s-l893/Automotive-Telemetry-Data-Acquisition-System-Black-Box-/BlackBox_V2/Core/Src/display.c

/*
 * display.c
 *
 *  Created on: Sep 11, 2026
 *      Author: Sunny Lin
 */
#include "display.h"
#include "main.h"
#include "spi.h"
#include "sd_spi_bus.h"
#include "iwdg.h"

#include <stdint.h>

#define DISPLAY_CS_PIN        GPIO_PIN_14
#define DISPLAY_CS_GPIO_PORT  GPIOB
#define DISPLAY_DC_PIN        DC_SPI1_Pin
#define DISPLAY_DC_GPIO_PORT  DC_SPI1_GPIO_Port
#define DISPLAY_RST_PIN       RESET_SPI1_Pin
#define DISPLAY_RST_GPIO_PORT RESET_SPI1_GPIO_Port
#define NATIVE_WIDTH 240
#define NATIVE_HEIGHT 320
#define LOGICAL_WIDTH  320  // done for custom function to remap points as bitwise toggle for MV MADCT1 doesnt work on chinese branded ili9341
#define LOGICAL_HEIGHT 240

/*
 * LCD bring-up notes:
 * - Nucleo: SB13/SB14 OFF, SB62/SB63 ON so PA2/PA3 reach the headers (HW).
 * - PA2/PA3 are LCD DC/RESET — do not enable USART2 on those pins.
 * - SD disk init leaves SPI1 in Mode3 — reconfig Mode0 before LCD traffic.
 * - Fill buffer is static: default MSP stack is only 1KB.
 * - PB14 (LCD_CS) is in the .ioc but was never emitted into gpio.c.
 */

static void LCD_BusPrepare(void) // SPI1 back into mode 0
{
	GPIO_InitTypeDef GPIO_InitStruct = {0};

	/* USART2 must not own PA2/PA3 (DC/RESET) */
	__HAL_RCC_USART2_CLK_ENABLE();
	__HAL_RCC_USART2_FORCE_RESET();
	__HAL_RCC_USART2_RELEASE_RESET();
	__HAL_RCC_USART2_CLK_DISABLE();

	SD_CS_ForceIdleHigh();

	__HAL_RCC_GPIOA_CLK_ENABLE();
	__HAL_RCC_GPIOB_CLK_ENABLE();

	HAL_GPIO_WritePin(DISPLAY_CS_GPIO_PORT, DISPLAY_CS_PIN, GPIO_PIN_SET);
	HAL_GPIO_WritePin(DISPLAY_DC_GPIO_PORT, DISPLAY_DC_PIN, GPIO_PIN_RESET);
	HAL_GPIO_WritePin(DISPLAY_RST_GPIO_PORT, DISPLAY_RST_PIN, GPIO_PIN_SET);

	GPIO_InitStruct.Pin = DISPLAY_CS_PIN;
	GPIO_InitStruct.Mode = GPIO_MODE_OUTPUT_PP;
	GPIO_InitStruct.Pull = GPIO_NOPULL;
	GPIO_InitStruct.Speed = GPIO_SPEED_FREQ_HIGH;
	HAL_GPIO_Init(DISPLAY_CS_GPIO_PORT, &GPIO_InitStruct);

	GPIO_InitStruct.Pin = DISPLAY_DC_PIN | DISPLAY_RST_PIN;
	GPIO_InitStruct.Speed = GPIO_SPEED_FREQ_LOW;
	HAL_GPIO_Init(DISPLAY_DC_GPIO_PORT, &GPIO_InitStruct);
	GPIOA->AFR[0] &= ~(0xFFu << (2 * 4)); /* clear USART2 AF on PA2/PA3 */

	/* ILI9341: SPI Mode0 (SD path may have left Mode3) */
	SD_SPI_Reconfig(SPI_BAUDRATEPRESCALER_8, SPI_POLARITY_LOW, SPI_PHASE_1EDGE);
}

/* HELPER GPIO TOGGLE FUNCTIONS FOR CS, DC, RESET */

static void LCD_CS_High(void)
{
	HAL_GPIO_WritePin(DISPLAY_CS_GPIO_PORT, DISPLAY_CS_PIN, GPIO_PIN_SET);
}

static void LCD_CS_Low(void)
{
	HAL_GPIO_WritePin(DISPLAY_CS_GPIO_PORT, DISPLAY_CS_PIN, GPIO_PIN_RESET);
}

static void LCD_DC_High(void)	/* DC REQUIRED TO BE PULLED HIGH FOR DATA */
{
	HAL_GPIO_WritePin(DISPLAY_DC_GPIO_PORT, DISPLAY_DC_PIN, GPIO_PIN_SET);
}

static void LCD_DC_Low(void)	/* DC REQUIRED TO BE PULLED LOW FOR COMMANDS */
{
	HAL_GPIO_WritePin(DISPLAY_DC_GPIO_PORT, DISPLAY_DC_PIN, GPIO_PIN_RESET);
}

static void LCD_RST_Low(void)
{
	HAL_GPIO_WritePin(DISPLAY_RST_GPIO_PORT, DISPLAY_RST_PIN, GPIO_PIN_RESET);
}

static void LCD_RST_High(void)
{
	HAL_GPIO_WritePin(DISPLAY_RST_GPIO_PORT, DISPLAY_RST_PIN, GPIO_PIN_SET);
}

/* SEND BYTE TO ILI9341 */
void LCD_Send_Command(uint8_t cmd, uint8_t *params, int param_count)
{
	SD_SPI_Reconfig(SPI_BAUDRATEPRESCALER_8, SPI_POLARITY_LOW, SPI_PHASE_1EDGE); // toggle spi1 back to mode 0
	LCD_CS_Low();
	LCD_DC_Low();
	HAL_SPI_Transmit(&hspi1, &cmd, 1, HAL_MAX_DELAY);
	if (param_count > 0) {
		LCD_DC_High();
		HAL_SPI_Transmit(&hspi1, params, param_count, HAL_MAX_DELAY);
	}
	LCD_CS_High();
}

void LCD_Hardware_Reset(void) // ILI9341 power up sequence
{
	LCD_RST_Low();
	HAL_Delay(15);
	LCD_RST_High();
	HAL_Delay(120);
}

void LCD_Init(void)
{
	LCD_BusPrepare();
	LCD_Hardware_Reset();
	LCD_Send_Command(0x11, NULL, 0);
	HAL_Delay(120); /* blocking delays used in init sequence (reset included) */
	uint8_t pixel_format = 0x55;
	LCD_Send_Command(0x3A, &pixel_format, 1);
	uint8_t madct1 = 0x48;
	LCD_Send_Command(0x36, &madct1, 1);
	LCD_Send_Command(0x29, NULL, 0);
	HAL_Delay(33);
}

void LCD_SetWindow(uint16_t x0, uint16_t y0, uint16_t x1, uint16_t y1)
{
	uint8_t col_params[4];
	/* fill col_params using x0/x1 high/low bytes, send via 0x2A (CASET) */
	col_params[0] = x0 >> 8;
	col_params[1] = x0 & 0xFF;
	col_params[2] = x1 >> 8;
	col_params[3] = x1 & 0xFF;
	LCD_Send_Command(0x2A, col_params, 4);
	uint8_t row_params[4];
	row_params[0] = y0 >> 8;
	row_params[1] = y0 & 0xFF;
	row_params[2] = y1 >> 8;
	row_params[3] = y1 & 0xFF;
	LCD_Send_Command(0x2B, row_params, 4);
	/* fill row_params using y0/y1 high/low bytes, send via 0x2B (PASET) */
}

void LCD_SetWindow_Logical(uint16_t lx0, uint16_t ly0, uint16_t lx1, uint16_t ly1){
	uint16_t x0_start = lx0;
	uint16_t y0_start = ly0;
	uint16_t x1_start = lx1;
	uint16_t y1_start = ly1;

	uint16_t x0_end = (LOGICAL_HEIGHT - 1) - y0_start;
	uint16_t y0_end = ((NATIVE_HEIGHT - 1) - x0_start);

	uint16_t x1_end = (LOGICAL_HEIGHT - 1) - y1_start;
	uint16_t y1_end = ((NATIVE_HEIGHT - 1) - x1_start); 	// consistent formula for a 90 degree rotation

	if(y1_end < y0_end){		// ensures correct coordinate order
		uint16_t temp = y1_end;
		y1_end = y0_end;
		y0_end = temp;
	}

	if(x1_end < x0_end){		// ensures correct coordinate order
		uint16_t temp = x1_end;
		x1_end = x0_end;
		x0_end = temp;
	}

	LCD_SetWindow(x0_end, y0_end, x1_end, y1_end);
}

static void LCD_Send_Data(uint8_t *data, uint32_t size)
{
	HAL_SPI_Transmit(&hspi1, data, size, HAL_MAX_DELAY);
}

void LCD_FillScreen(uint16_t colour)
{
	/* static: 640B on a 1KB MSP stack HardFaults mid-fill */
	static uint8_t colour_buffer[640];
	uint8_t ramwr = 0x2C;
	int k;

	LCD_SetWindow_Logical(0, 0, LOGICAL_WIDTH - 1, LOGICAL_HEIGHT - 1);

	LCD_CS_Low();
	LCD_DC_Low();
	HAL_SPI_Transmit(&hspi1, &ramwr, 1, HAL_MAX_DELAY);
	LCD_DC_High();

	/* SPLIT UINT16T VARIABLE INTO UINT8T INTO ARRAY — one row (320 px) */
	for (k = 0; k < 640; k++) {
		if (k % 2 == 0) {
			colour_buffer[k] = colour >> 8;
		} else {
			colour_buffer[k] = colour & 0xFF;
		}
	}

	for (k = 0; k < LOGICAL_HEIGHT; k++) {
		LCD_Send_Data(colour_buffer, 640);
		if ((k & 0x1F) == 0) {
			HAL_IWDG_Refresh(&hiwdg);
		}
	}

	LCD_CS_High();
}

void LCD_FillRect(uint16_t x, uint16_t y, uint16_t w, uint16_t h, uint16_t colour){
	LCD_SetWindow_Logical(x, y, x + w - 1, y + h - 1);
	uint8_t ramwr = 0x2C;
	LCD_CS_Low();
	LCD_DC_Low();
	HAL_SPI_Transmit(&hspi1, &ramwr, 1, HAL_MAX_DELAY); // memory write mode
	LCD_DC_High();
	static uint8_t rect[2000]; // colour data for rectangle
	for (int i = 0; i < 2000; i++){
		if (i % 2 == 0){
			rect[i] = colour >> 8;
		}
		else{
			rect[i] = colour & 0xFF;

		}
	}
	uint32_t total_bytes = w * h * 2;
	uint32_t full_chunks = total_bytes / 2000;
	uint32_t leftover = total_bytes % 2000;

	for (int k = 0; k < full_chunks; k++){
		LCD_Send_Data(rect, 2000);
		if (k % 32 == 0){
			HAL_IWDG_Refresh(&hiwdg);
		}
	}

	if (leftover != 0){
		LCD_Send_Data(rect, leftover);
	}


	LCD_CS_High();
}

void LCD_DrawRect(uint16_t x, uint16_t y, uint16_t w, uint16_t h, uint16_t colour)
{
	if (w == 0 || h == 0) {
		return;
	}
	LCD_FillRect(x, y, w, 1, colour);
	LCD_FillRect(x, (uint16_t)(y + h - 1), w, 1, colour);
	LCD_FillRect(x, y, 1, h, colour);
	LCD_FillRect((uint16_t)(x + w - 1), y, 1, h, colour);
}

/* 8x8 GLCD-style font (ASCII 32..127): each byte is a column, bit0 = top */
static const uint8_t font8x8_basic[96][8] = {
	{0x00,0x00,0x00,0x00,0x00,0x00,0x00,0x00}, {0x00,0x00,0x5F,0x00,0x00,0x00,0x00,0x00},
	{0x00,0x07,0x00,0x07,0x00,0x00,0x00,0x00}, {0x14,0x7F,0x14,0x7F,0x14,0x00,0x00,0x00},
	{0x24,0x2A,0x7F,0x2A,0x12,0x00,0x00,0x00}, {0x23,0x13,0x08,0x64,0x62,0x00,0x00,0x00},
	{0x36,0x49,0x55,0x22,0x50,0x00,0x00,0x00}, {0x00,0x05,0x03,0x00,0x00,0x00,0x00,0x00},
	{0x00,0x1C,0x22,0x41,0x00,0x00,0x00,0x00}, {0x00,0x41,0x22,0x1C,0x00,0x00,0x00,0x00},
	{0x08,0x2A,0x1C,0x2A,0x08,0x00,0x00,0x00}, {0x08,0x08,0x3E,0x08,0x08,0x00,0x00,0x00},
	{0x00,0x50,0x30,0x00,0x00,0x00,0x00,0x00}, {0x08,0x08,0x08,0x08,0x08,0x00,0x00,0x00},
	{0x00,0x60,0x60,0x00,0x00,0x00,0x00,0x00}, {0x20,0x10,0x08,0x04,0x02,0x00,0x00,0x00},
	{0x3E,0x51,0x49,0x45,0x3E,0x00,0x00,0x00}, {0x00,0x42,0x7F,0x40,0x00,0x00,0x00,0x00},
	{0x42,0x61,0x51,0x49,0x46,0x00,0x00,0x00}, {0x21,0x41,0x45,0x4B,0x31,0x00,0x00,0x00},
	{0x18,0x14,0x12,0x7F,0x10,0x00,0x00,0x00}, {0x27,0x45,0x45,0x45,0x39,0x00,0x00,0x00},
	{0x3C,0x4A,0x49,0x49,0x30,0x00,0x00,0x00}, {0x01,0x71,0x09,0x05,0x03,0x00,0x00,0x00},
	{0x36,0x49,0x49,0x49,0x36,0x00,0x00,0x00}, {0x06,0x49,0x49,0x29,0x1E,0x00,0x00,0x00},
	{0x00,0x36,0x36,0x00,0x00,0x00,0x00,0x00}, {0x00,0x56,0x36,0x00,0x00,0x00,0x00,0x00},
	{0x00,0x08,0x14,0x22,0x41,0x00,0x00,0x00}, {0x14,0x14,0x14,0x14,0x14,0x00,0x00,0x00},
	{0x41,0x22,0x14,0x08,0x00,0x00,0x00,0x00}, {0x02,0x01,0x51,0x09,0x06,0x00,0x00,0x00},
	{0x32,0x49,0x79,0x41,0x3E,0x00,0x00,0x00}, {0x7E,0x11,0x11,0x11,0x7E,0x00,0x00,0x00},
	{0x7F,0x49,0x49,0x49,0x36,0x00,0x00,0x00}, {0x3E,0x41,0x41,0x41,0x22,0x00,0x00,0x00},
	{0x7F,0x41,0x41,0x22,0x1C,0x00,0x00,0x00}, {0x7F,0x49,0x49,0x49,0x41,0x00,0x00,0x00},
	{0x7F,0x09,0x09,0x09,0x01,0x00,0x00,0x00}, {0x3E,0x41,0x49,0x49,0x7A,0x00,0x00,0x00},
	{0x7F,0x08,0x08,0x08,0x7F,0x00,0x00,0x00}, {0x00,0x41,0x7F,0x41,0x00,0x00,0x00,0x00},
	{0x20,0x40,0x41,0x3F,0x01,0x00,0x00,0x00}, {0x7F,0x08,0x14,0x22,0x41,0x00,0x00,0x00},
	{0x7F,0x40,0x40,0x40,0x40,0x00,0x00,0x00}, {0x7F,0x02,0x0C,0x02,0x7F,0x00,0x00,0x00},
	{0x7F,0x04,0x08,0x10,0x7F,0x00,0x00,0x00}, {0x3E,0x41,0x41,0x41,0x3E,0x00,0x00,0x00},
	{0x7F,0x09,0x09,0x09,0x06,0x00,0x00,0x00}, {0x3E,0x41,0x51,0x21,0x5E,0x00,0x00,0x00},
	{0x7F,0x09,0x19,0x29,0x46,0x00,0x00,0x00}, {0x46,0x49,0x49,0x49,0x31,0x00,0x00,0x00},
	{0x01,0x01,0x7F,0x01,0x01,0x00,0x00,0x00}, {0x3F,0x40,0x40,0x40,0x3F,0x00,0x00,0x00},
	{0x1F,0x20,0x40,0x20,0x1F,0x00,0x00,0x00}, {0x3F,0x40,0x38,0x40,0x3F,0x00,0x00,0x00},
	{0x63,0x14,0x08,0x14,0x63,0x00,0x00,0x00}, {0x07,0x08,0x70,0x08,0x07,0x00,0x00,0x00},
	{0x61,0x51,0x49,0x45,0x43,0x00,0x00,0x00}, {0x00,0x7F,0x41,0x41,0x00,0x00,0x00,0x00},
	{0x02,0x04,0x08,0x10,0x20,0x00,0x00,0x00}, {0x00,0x41,0x41,0x7F,0x00,0x00,0x00,0x00},
	{0x04,0x02,0x01,0x02,0x04,0x00,0x00,0x00}, {0x40,0x40,0x40,0x40,0x40,0x00,0x00,0x00},
	{0x00,0x01,0x02,0x04,0x00,0x00,0x00,0x00}, {0x20,0x54,0x54,0x54,0x78,0x00,0x00,0x00},
	{0x7F,0x48,0x44,0x44,0x38,0x00,0x00,0x00}, {0x38,0x44,0x44,0x44,0x20,0x00,0x00,0x00},
	{0x38,0x44,0x44,0x48,0x7F,0x00,0x00,0x00}, {0x38,0x54,0x54,0x54,0x18,0x00,0x00,0x00},
	{0x08,0x7E,0x09,0x01,0x02,0x00,0x00,0x00}, {0x08,0x14,0x54,0x54,0x3C,0x00,0x00,0x00},
	{0x7F,0x08,0x04,0x04,0x78,0x00,0x00,0x00}, {0x00,0x44,0x7D,0x40,0x00,0x00,0x00,0x00},
	{0x20,0x40,0x44,0x3D,0x00,0x00,0x00,0x00}, {0x7F,0x10,0x28,0x44,0x00,0x00,0x00,0x00},
	{0x00,0x41,0x7F,0x40,0x00,0x00,0x00,0x00}, {0x7C,0x04,0x18,0x04,0x78,0x00,0x00,0x00},
	{0x7C,0x08,0x04,0x04,0x78,0x00,0x00,0x00}, {0x38,0x44,0x44,0x44,0x38,0x00,0x00,0x00},
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
};

void LCD_DrawChar(uint16_t x, uint16_t y, char c, uint16_t fg, uint16_t bg, uint8_t scale)
{
	uint8_t ramwr = 0x2C;
	uint16_t gw;
	uint16_t gh;
	const uint8_t *glyph;
	uint8_t strip[80];
	uint8_t fg_hi = (uint8_t)(fg >> 8);
	uint8_t fg_lo = (uint8_t)(fg & 0xFF);
	uint8_t bg_hi = (uint8_t)(bg >> 8);
	uint8_t bg_lo = (uint8_t)(bg & 0xFF);

	if (scale == 0) {
		scale = 1;
	}
	if (scale > 5) {
		scale = 5;
	}
	if (c < 32 || c > 127) {
		c = '?';
	}

	glyph = font8x8_basic[c - 32];
	gw = (uint16_t)(8U * scale);
	gh = (uint16_t)(8U * scale);

	if ((uint32_t)x + gw > LCD_WIDTH || (uint32_t)y + gh > LCD_HEIGHT) {
		return;
	}

	/*
	 * SetWindow_Logical maps landscape -> native with both axes inverted.
	 * Hardware fill order is columns right->left, within each column bottom->top.
	 */
	LCD_SetWindow_Logical(x, y, (uint16_t)(x + gw - 1U), (uint16_t)(y + gh - 1U));
	LCD_CS_Low();
	LCD_DC_Low();
	HAL_SPI_Transmit(&hspi1, &ramwr, 1, HAL_MAX_DELAY);
	LCD_DC_High();

	for (int8_t col = 7; col >= 0; col--) {
		for (int8_t sx = (int8_t)scale - 1; sx >= 0; sx--) {
			uint16_t o = 0;
			for (int8_t row = 7; row >= 0; row--) {
				uint8_t on = (glyph[(uint8_t)col] & (1U << (uint8_t)row)) ? 1U : 0U;
				uint8_t hi = on ? fg_hi : bg_hi;
				uint8_t lo = on ? fg_lo : bg_lo;
				for (int8_t sy = (int8_t)scale - 1; sy >= 0; sy--) {
					strip[o++] = hi;
					strip[o++] = lo;
					(void)sy;
				}
			}
			LCD_Send_Data(strip, o);
			(void)sx;
		}
		HAL_IWDG_Refresh(&hiwdg);
	}

	LCD_CS_High();
}

void LCD_DrawString(uint16_t x, uint16_t y, const char *s, uint16_t fg, uint16_t bg, uint8_t scale)
{
	uint16_t cx = x;
	uint16_t advance = (uint16_t)(8U * (scale ? scale : 1U));

	if (s == NULL) {
		return;
	}
	while (*s) {
		LCD_DrawChar(cx, y, *s, fg, bg, scale);
		cx = (uint16_t)(cx + advance);
		if (cx >= LCD_WIDTH) {
			break;
		}
		s++;
	}
}

void LCD_DrawTextField(uint16_t x, uint16_t y, uint16_t w, uint16_t h,
		uint16_t bg, uint16_t fg, uint8_t scale, const char *s)
{
	LCD_FillRect(x, y, w, h, bg);
	LCD_DrawString(x, y, s, fg, bg, scale);
	HAL_IWDG_Refresh(&hiwdg);
}

void LCD_DrawBitmap1bpp(uint16_t x, uint16_t y, uint16_t w, uint16_t h,
		const uint8_t *bits, uint16_t fg, uint16_t bg)
{
	uint8_t ramwr = 0x2C;
	uint16_t row_bytes;
	uint8_t strip[64];
	uint8_t fg_hi = (uint8_t)(fg >> 8);
	uint8_t fg_lo = (uint8_t)(fg & 0xFF);
	uint8_t bg_hi = (uint8_t)(bg >> 8);
	uint8_t bg_lo = (uint8_t)(bg & 0xFF);

	if (bits == NULL || w == 0 || h == 0) {
		return;
	}
	if ((uint32_t)x + w > LCD_WIDTH || (uint32_t)y + h > LCD_HEIGHT) {
		return;
	}
	if (h > 32) {
		return;
	}

	row_bytes = (uint16_t)((w + 7U) / 8U);
	LCD_SetWindow_Logical(x, y, (uint16_t)(x + w - 1U), (uint16_t)(y + h - 1U));
	LCD_CS_Low();
	LCD_DC_Low();
	HAL_SPI_Transmit(&hspi1, &ramwr, 1, HAL_MAX_DELAY);
	LCD_DC_High();

	for (int16_t col = (int16_t)w - 1; col >= 0; col--) {
		uint16_t o = 0;
		for (int16_t row = (int16_t)h - 1; row >= 0; row--) {
			const uint8_t *rowptr = bits + ((uint16_t)row * row_bytes);
			uint8_t byte = rowptr[(uint16_t)col / 8U];
			uint8_t on = (byte & (0x80U >> ((uint16_t)col & 7U))) ? 1U : 0U;
			strip[o++] = on ? fg_hi : bg_hi;
			strip[o++] = on ? fg_lo : bg_lo;
		}
		LCD_Send_Data(strip, o);
	}

	LCD_CS_High();
}
