s-l893/Automotive-Telemetry-Data-Acquisition-System-Black-Box-/BlackBox_V2/Core/Src/fsm_sys.c

/*
 * fsm_sys.c
 *
 *  Created on: Jul 7, 2026
 *      Author: Sunny Lin
 *
 */

#include "can_handler.h"
#include "sd_logger.h"
#include "fault.h"
#include "fsm_sys.h"
#include <stdbool.h>
#include <stdint.h>
#include "main.h"
#include "imu.h"
#include "gps_driver.h"
#include "touch_driver.h"
#include "fsm_ui.h"
#include "can_ring_buffer.h"

#define IDLE_SHUTDOWN_TIMEOUT_MS 300000
#define SYNC_TIMEOUT_MS			 1500

// VARIABLE DECLARATION
static bool shutdown_complete = false;
uint32_t sync_timer = 0;
// FSM STRUCT DECLARED IN HEADER

sys_state_t current_state = SYS_INIT; // SET INITIAL STATE

void SYS_FSM_TICK(void){
    uint32_t can_timer;

    switch (current_state){
    case SYS_INIT:
        if (!sd_mount){
            fault_flags.sd_fault = true;
        }
        // enter idle so that UI and CAN still function
        if (peripherals_init || !sd_mount){
            current_state = SYS_IDLE;
        }
        break;
    case SYS_IDLE:
        imu_read();
        GPS_Driver_Update();
        Touch_Update();
        UI_FSM_Tick();
        if (can_frame_received_flag){
            current_state = SYS_LOGGING;
            UI_ResetSessionPeaks();
            if (sd_mount) {
                start_new_session_file();
            }
            last_can_frame = HAL_GetTick();
        }
        else{
            uint32_t idle_timer = HAL_GetTick();
            if ((idle_timer - last_can_frame) >= IDLE_SHUTDOWN_TIMEOUT_MS){
                current_state = SYS_SHUTDOWN;
            }
        }
        break;
    case SYS_LOGGING:
        if (can_frame_received_flag){
            last_can_frame = HAL_GetTick();
            can_frame_received_flag = false;
        }
        else{
            can_timer = HAL_GetTick(); // NON BLOCKING ARCHITECTURE
            if ((can_timer - last_can_frame) >= 2500){ // 2.5S SILENCE TIMEOUT FEATURE
                if (sd_mount) {
                    close_session_file();
                }
                current_state = SYS_IDLE;
            }
        }

        if (sd_mount) {
            SD_Logger_DrainCAN(); // DRAIN CAN RB FROM HERE
        } else {

            can_frame_t drop;
            while (CANRingBuffer_Pop(&can_rb, &drop)) {
            }
        }
        GPS_Driver_Update();
        imu_read(); // READ IMU DATA
        Touch_Update();
        UI_FSM_Tick();
        if (sd_mount && (HAL_GetTick() - sync_timer > SYNC_TIMEOUT_MS)) {
        	SD_Logger_Sync();
        	sync_timer = HAL_GetTick();
        }

        break;

    case SYS_FAULT:
        UI_FSM_Tick();
        imu_read();
        sd_recovery(); // ATTEMPT TO RETRY SD MOUNT
        if (sd_mount){
            current_state = SYS_IDLE;
        }
        break;
    case SYS_SHUTDOWN:
        if (!shutdown_complete){
            flush_ring_buffers(); // CLEAR CIRCULAR BUFFERS
            close_session_file(); // CLEANLY EXIT SD CARD FILE
            unmount_sd();
            shutdown_complete = true;
        }
        break;
        // FOLLOWING THIS BOARD WILL LOSE POWER
    default: // UNDEFINED BEHAVIOR
        current_state = SYS_FAULT;
    }
}
