s-l893/Automotive-Telemetry-Data-Acquisition-System-Black-Box-/BlackBox_V2/Core/Inc/fsm_ui.h

/*
 * fsm_ui.h
 *
 *  Created on: Jul 7, 2026
 *      Author: Sunny Lin
 */

#ifndef INC_FSM_UI_H_
#define INC_FSM_UI_H_

void UI_Init(void);
void UI_FSM_Tick(void);
void UI_ResetSessionPeaks(void);

#endif /* INC_FSM_UI_H_ */
